andrewsargent2311-web/paraglide_vario_ESP32/paraglide_vario_ESP32/Goes into SD card/roy_real_crop_preview.png

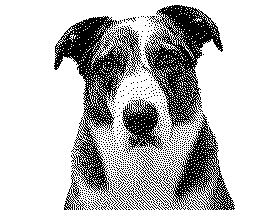
paraglide_vario_ESP32/Goes into SD card/roy_real_crop_preview.png
