andrewsargent2311-web/paraglide_vario_ESP32/Photos/20260914_193758.jpg

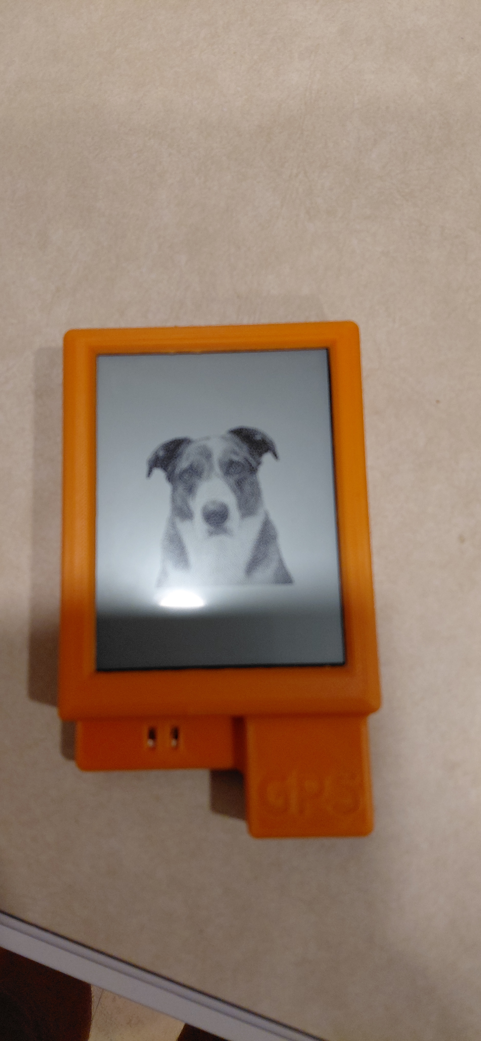
Photos/20260914_193758.jpg
