andrewsargent2311-web/paraglide_vario_ESP32/Photos/20260914_193810.jpg

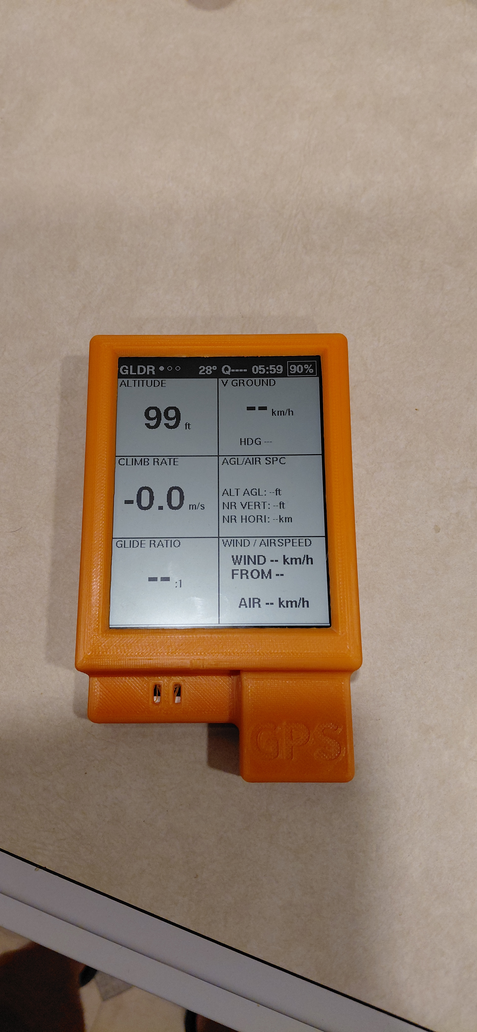
Photos/20260914_193810.jpg
