andrewsargent2311-web/paraglide_vario_ESP32/Photos/20260916_142536.jpg

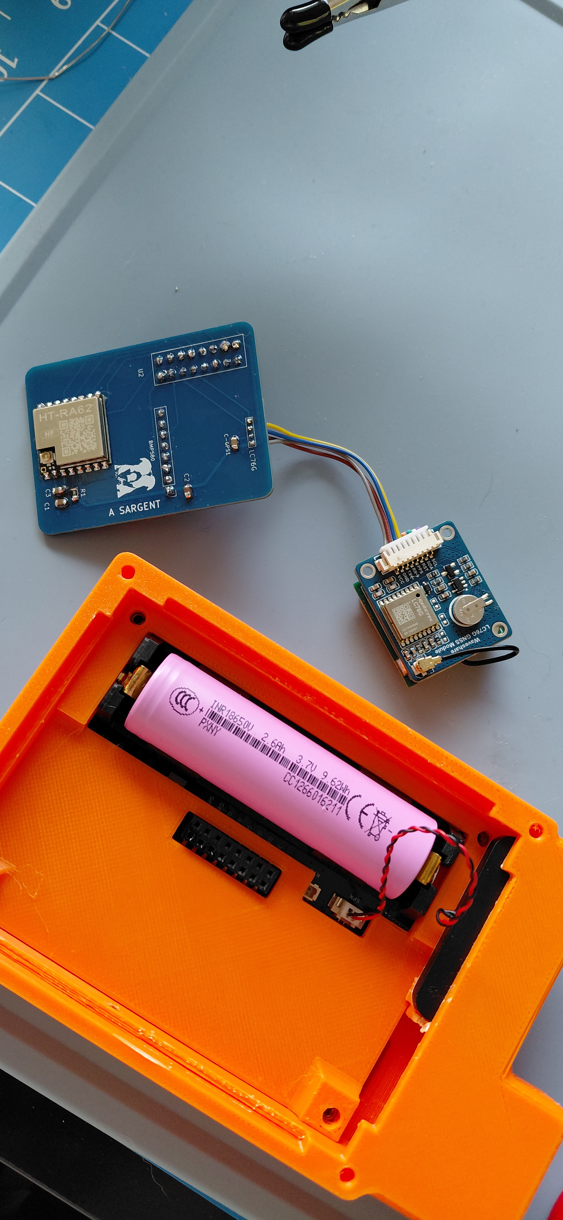
Photos/20260916_142536.jpg
