andrewsargent2311-web/paraglide_vario_ESP32/Photos/20260917_093752.jpg

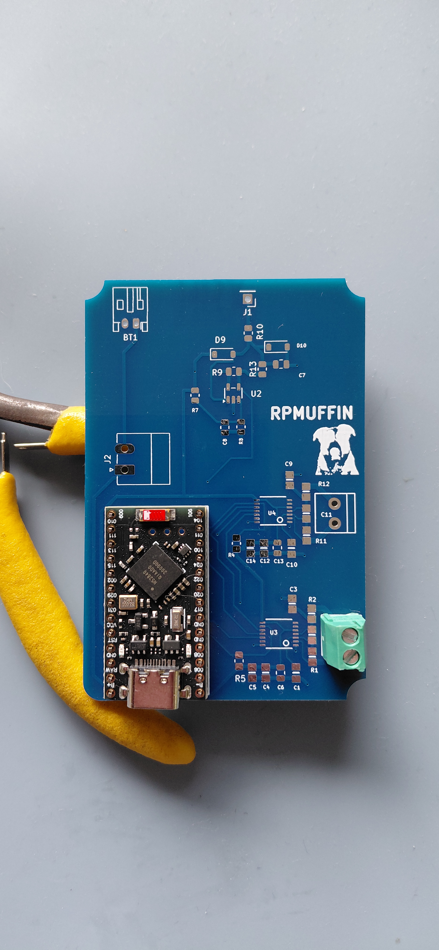
Photos/20260917_093752.jpg
