andrewsargent2311-web/paraglide_vario_ESP32/Photos/20260919_101642.jpg

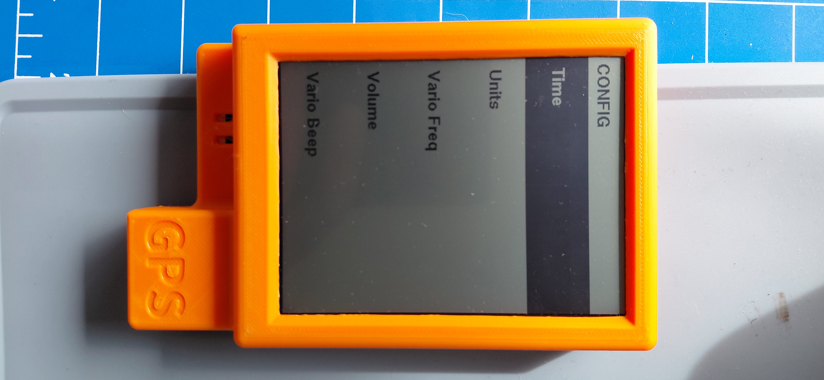
Photos/20260919_101642.jpg
