andrewsargent2311-web/paraglide_vario_ESP32/paraglide_vario_ESP32/menu.h

#ifndef MENU_H
#define MENU_H

#include <Arduino.h>
#include <U8g2lib.h>
#include "settings.h"

// =====================================================
// Display geometry. Duplicated (identically) from the main .ino so this
// header is self-contained -- see the derivation notes next to SCREEN_W/
// SCREEN_H in the .ino if that panel geometry ever changes.
// =====================================================
#define SCREEN_W 300
#define SCREEN_H 400

// =====================================================
// PAGES
// The actual page-drawing functions (drawParagliderPage() etc.) still live
// in the main .ino -- this type/state lives here because the menu needs to
// read and write it ("Main Page" submenu swaps the active main page).
// =====================================================
enum Page { PAGE_PARAGLIDER = 0,
            PAGE_WEATHER,
            PAGE_ADSB,
            PAGE_PARAMOTOR,
            PAGE_COUNT };

// Only 3 pages are cycled through with a short press. Slot 0 is the "main"
// page and is swappable between Paraglider and Paramotor from the menu;
// slots 1 and 2 are fixed at Weather and ADS-B.
#define ACTIVE_PAGE_COUNT 3

extern Page currentPage;
extern const char* PAGE_NAMES[PAGE_COUNT];
extern Page activePages[ACTIVE_PAGE_COUNT];
extern uint8_t activePageIndex;

// =====================================================
// MENU SCREENS
// The menu is a small tree, navigated with a stack (see menu.cpp):
//   MAIN
//   |-- MAIN_PAGE_SELECT  (Paraglider / Paramotor)
//   |-- CONFIG
//   |     |-- CONFIG_TIME     ("NZ (Auto)" DST-aware default, or a fixed
//   |     |                    manual UTC offset from -12 to +14 hours)
//   |     |-- UNITS           (Altitude / Speed, cycled in place)
//   |     |-- CONFIG_VOLUME   (main buzzer volume, 10-100% in 10% steps,
//   |     |                    dB-scaled: 100% = +12dB, 3dB per step)
//   |     |-- VARIO_BEEP
//   |     |     |-- VARIO_BEEP_CLIMB_VOL   (climb beep volume, 0-100%
//   |     |     |                           in 10% steps, dB-scaled)
//   |     |     `-- VARIO_BEEP_SINK_VOL    (sink tone volume, same scale)
//   |     `-- SCREEN          ("GPS Top" / "GPS Bottom" -- 180-degree
//   |                          display flip; see applyScreenOrientation())
//   |-- CONNECTIONS
//   |     |-- WIFI              (On/Off toggle, cycled in place --
//   |     |                      persisted; see setWifiRadioEnabled()
//   |     |                      (wifi_manager.h) -- then pick a saved
//   |     |                      network -- see secrets.h; choice is
//   |     |                      remembered across reboots)
//   |     |-- BLUETOOTH
//   |     |     |-- (On/Off toggle, cycled in place)
//   |     |     |-- SCAN        (live-updating list of nearby BLE
//   |     |     |                devices -- select one to connect; this
//   |     |     |                board is BLE-only, no Classic BT)
//   |     |     `-- (Forget Device -- only actionable once one's saved)
//   |     `-- FANET            (On/Off, cycled in place -- actually
//   |                            sleeps/wakes the SX1262, not just the
//   |                            software stack; see setFanetEnabled())
//   |-- FANET_MESSAGING  (On/Off toggle, persisted; see
//   |                      fanetMessagingEnabled in settings.h --
//   |                      plus one item per preset message,
//   |                      selecting one broadcasts it
//   |                      immediately. Broadcast only, no
//   |                      addressed messages -- see
//   |                      FanetMessaging.h/Fanet.h. Preset
//   |                      wording is compiled-in, not editable
//   |                      from the device -- no keyboard)
//   |-- MAP                (list of *.ADEM files found on the SD card)
//   |-- ADSB_SETTINGS
//   |     |-- ADSB_RADIUS       (horizontal alert trigger distance)
//   |     |-- ADSB_VERTICAL     (vertical alert trigger distance)
//   |     |-- (Auto-Jump toggle, cycled in place)
//   |     |-- (Alarm Sound: Off/Alarm/Voice, cycled in place -- see
//   |     |    adsbAlarmMode in settings.h. Alarm is the existing 5s
//   |     |    two-tone siren; Voice speaks the nearest threat's clock
//   |     |    position, heading, altitude and distance instead -- see
//   |     |    triggerAdsbAlert()/VoiceAlert.h)
//   |     |-- ADSB_ALERT_VOLUME (0-100% in 10% steps, same dB scale as
//   |     |                      the vario volumes, plus a Test item
//   |     |                      that previews whichever of Alarm/Voice
//   |     |                      is currently selected at this volume)
//   |     |-- ADSB_RANGE_RINGS  (far/default range ring pair -- 15/30km,
//   |     |                      10/20km, 20/40km, or 30/60km)
//   |     |-- (Airspace Alert Bar toggle, cycled in place -- NOT
//   |     |    persisted, always back on at reboot; see
//   |     |    airspaceAlertBarEnabled in settings.h)
//   |     `-- (Airspace Info toggle, cycled in place -- persisted; see
//   |          airspaceInfoBarEnabled in settings.h. Shows/hides
//   |          drawAirspaceInfoBar() -- ADS-B page only, bottom of
//   |          screen, current airspace name/frequency including CFZ,
//   |          or "Class G" if not inside anything charted)
//   |-- WEATHER_SETTINGS
//   |     |-- WEATHER_POLL_INTERVAL   (Zephyr station poll cadence)
//   |     |-- WEATHER_STATIONS_SHOWN  (how many stations to display)
//   |     `-- WEATHER_SOURCE          ("FANET" / "Zephyr" -- preferred
//   |                                  Weather-page data source; falls
//   |                                  back to FANET regardless if the
//   |                                  preferred source has no data)
//   `-- FLIGHT_RECORDINGS
//         |-- (Recording toggle, cycled in place -- NOT persisted,
//         |    always back on at reboot; see flightRecorderEnabled in
//         |    settings.h. OFF cleanly closes any in-progress IGC file
//         |    rather than abandoning it -- see setFlightRecorderEnabled())
//         |-- EXPORT_FILES     (Start/Stop a read-only WiFi file server
//         |                      for downloading IGC logs -- see
//         |                      FileServer.h. Needs WiFi connected
//         |                      (Connections > WiFi) and the SD card
//         |                      mounted; shows the URL to browse to
//         |                      once running. Auto-stops after 15
//         |                      minutes idle -- see
//         |                      FILE_SERVER_IDLE_TIMEOUT_MS)
//         `-- (Auto-Stop toggle, cycled in place -- persisted, off by
//              default; see igcAutoStopEnabled in settings.h. When on,
//              recording stops itself once ground speed has stayed
//              below 5km/h for 20s -- see IGC_AUTOSTOP_SPEED_KPH /
//              IGC_AUTOSTOP_SUSTAIN_MS, main .ino)
//
// Gestures (see updatePageButton() in the main .ino):
//   short press  -- move the highlight down (wraps within the current screen)
//   hold 2s      -- select the highlighted item (enter a submenu, apply a
//                   value, or toggle a setting)
//   double press -- go back one level, or close the menu from the top level
// =====================================================
enum MenuScreen {
  MENU_SCREEN_MAIN = 0,
  MENU_SCREEN_MAIN_PAGE_SELECT,
  MENU_SCREEN_CONFIG,
  MENU_SCREEN_CONFIG_TIME,
  MENU_SCREEN_UNITS,
  MENU_SCREEN_CONFIG_VOLUME,
  MENU_SCREEN_VARIO_BEEP,
  MENU_SCREEN_VARIO_BEEP_CLIMB_VOL,
  MENU_SCREEN_VARIO_BEEP_SINK_VOL,
  MENU_SCREEN_SCREEN,
  MENU_SCREEN_CONNECTIONS,
  MENU_SCREEN_WIFI_LIST,
  MENU_SCREEN_BLUETOOTH,
  MENU_SCREEN_BLUETOOTH_SCAN,
  MENU_SCREEN_MAP,
  MENU_SCREEN_ADSB_SETTINGS,
  MENU_SCREEN_ADSB_RADIUS,
  MENU_SCREEN_ADSB_VERTICAL,
  MENU_SCREEN_ADSB_ALERT_VOLUME,
  MENU_SCREEN_ADSB_RANGE_RINGS,
  MENU_SCREEN_WEATHER_SETTINGS,
  MENU_SCREEN_WEATHER_POLL_INTERVAL,
  MENU_SCREEN_WEATHER_STATIONS_SHOWN,
  MENU_SCREEN_WEATHER_SOURCE,
  MENU_SCREEN_FLIGHT_RECORDINGS,
  MENU_SCREEN_EXPORT_FILES,
  MENU_SCREEN_FANET_MESSAGING
};

extern bool menuActive;
extern uint8_t menuSelectedIndex;

// A "double press" is two presses with less than this many ms between the
// first release and the second press-down; a 2s hold on an open menu
// selects the highlighted item. Consumed by updatePageButton() in the
// main .ino.
#define MENU_DOUBLE_PRESS_MS 800
#define MENU_SELECT_HOLD_MS 2000

// =====================================================
// MAP FILE SELECTION
// The Map screen scans the SD card root for *.ADEM tiles when opened (see
// scanMapFiles() in menu.cpp) and lets the pilot choose which one
// getGroundElevationM() should read from. selectedDemFile (DEM_FILENAME_MAX_LEN
// too) now lives in settings.h alongside every other persisted setting --
// this header pulls both in via the settings.h include above. It's read
// by the DEM lookup in the main .ino's background task, guarded by
// sdMutex -- always go through setSelectedDemFile() to change it, never
// assign it directly, or a scan running on the other core could read a
// half-written filename.
// =====================================================
void setSelectedDemFile(const char* filename);

// =====================================================
// Dependencies provided by the main .ino
// =====================================================
extern U8G2_ST7305_300X400_1_4W_HW_SPI u8g2;
extern bool sdCardOK;
extern SemaphoreHandle_t sdMutex;

// Set whenever page/menu state changes; drives an immediate redraw instead
// of waiting for the next 1Hz display tick.
extern bool displayDirty;

// Short non-blocking UI feedback tone (defined in the main .ino).
void playFeedbackTone(float freq, unsigned long durationMs);

// Same as playFeedbackTone(), but at the loudness that a climb/sink volume
// percentage (0-100) would produce -- lets Config > Vario Beep play the
// tone back at the level being picked (defined in the main .ino).
void playVolumePreviewTone(float freq, unsigned long durationMs, uint8_t volumePercent);

// Re-applies buzzerVolumePercent (settings.h) to the ES8311 codec's
// volume register -- call after changing it so the new level takes
// effect immediately (defined in the main .ino).
void applyBuzzerVolume();

// Actually enables/disables the SX1262 radio to match fanetEnabled
// (settings.h) -- sleeps/wakes the chip itself, not just the software
// FANET stack. If the radio was never successfully initialised (e.g. it
// was off at boot), enabling runs the full init sequence for the first
// time. Call after changing fanetEnabled so it takes effect immediately
// (defined in the main .ino).
void setFanetEnabled(bool enabled);

// Re-applies screenOrientation (settings.h) to the physical display via
// u8g2.setDisplayRotation() -- call after changing it so the flip takes
// effect immediately (defined in the main .ino).
void applyScreenOrientation();

// Turns the IGC flight recorder on/off (Flight Recordings > Recording).
// OFF cleanly closes any in-progress recording (see stopIgcRecording())
// rather than leaving the file open-but-dangling -- updateIgcRecorder()
// itself is gated on flightRecorderEnabled and would otherwise just stop
// being called at all, without ever reaching its normal
// landing-detected close path. Does NOT persist -- flightRecorderEnabled
// (settings.h) always resets to true at boot, same reasoning as
// airspaceAlertBarEnabled, so a flight can never go unrecorded just
// because recording was switched off during ground testing and never
// switched back on. Call after changing flightRecorderEnabled so it
// takes effect immediately (defined in the main .ino).
void setFlightRecorderEnabled(bool enabled);

// =====================================================
// Menu functions
// =====================================================
void openMenu();
void closeMenu();
void menuMoveDown();
void menuSelectCurrentItem();
void menuGoBack();
void drawMenu();

#endif  // MENU_H
