andrewsargent2311-web/paraglide_vario_ESP32/paraglide_vario_ESP32/settings.cpp

#include "settings.h"
#include <Preferences.h>

static Preferences prefs;

// Defaults match the values the display code used to have hard-coded:
// altitude in feet, ground speed in km/h.
AltitudeUnit altitudeUnit = ALT_UNIT_FEET;
SpeedUnit speedUnit = SPEED_UNIT_KMH;

// Default matches the app's original behaviour: automatic NZ time with
// DST applied. utcOffsetHours only takes effect once the pilot picks a
// manual entry from the Time menu.
TimeZoneMode timeZoneMode = TZ_MODE_AUTO_NZ;
int8_t utcOffsetHours = 12;

void getPilotLocalTime(struct tm* outTm) {
  time_t now;
  time(&now);

  if (timeZoneMode == TZ_MODE_MANUAL) {
    // Shift the UTC epoch by the fixed offset and read it back out with
    // gmtime_r() (not localtime_r()) so the NZ_TIMEZONE DST rule set at
    // boot never gets applied on top of it.
    time_t shifted = now + (time_t)utcOffsetHours * 3600L;
    gmtime_r(&shifted, outTm);
  } else {
    // NZ_TIMEZONE (set once via setenv("TZ", ...) in the main .ino's
    // setup()) already encodes the DST transition rule, so localtime_r()
    // handles the adjustment automatically.
    localtime_r(&now, outTm);
  }
}

float altitudeToDisplay(float meters) {
  return (altitudeUnit == ALT_UNIT_FEET) ? (meters * 3.28084f) : meters;
}

const char* altitudeUnitLabel() {
  return (altitudeUnit == ALT_UNIT_FEET) ? "ft" : "m";
}

float speedKphToDisplay(float kph) {
  switch (speedUnit) {
    case SPEED_UNIT_MS: return kph / 3.6f;
    case SPEED_UNIT_MPH: return kph * 0.621371f;
    default: return kph;  // SPEED_UNIT_KMH
  }
}

const char* speedUnitLabel() {
  switch (speedUnit) {
    case SPEED_UNIT_MS: return "m/s";
    case SPEED_UNIT_MPH: return "mph";
    default: return "km/h";  // SPEED_UNIT_KMH
  }
}

// Defaults match the values that used to be hard-coded (100/500/100/400).
unsigned long climbGapMinMs = 100UL;
unsigned long climbGapMaxMs = 500UL;
unsigned long climbPulseMinMs = 100UL;
unsigned long climbPulseMaxMs = 400UL;

// Default approximates the original hard-coded ES8311 register value
// (0xBF of 0xFF, ~75%) at the nearest 20% step.
uint8_t buzzerVolumePercent = 80;

// Defaults match the values that used to be hard-coded: 5km/2000ft threat
// trigger, auto-jump on, alarm audible, weather polled every 5 minutes,
// 4 stations shown.
float adsbAlertRadiusKm = 5.0f;
float adsbAlertVerticalFt = 2000.0f;
bool adsbAutoJumpEnabled = true;
uint8_t adsbAlarmMode = ADSB_ALARM_TONE;  // preserves the old default (alarm audible, not muted)
uint8_t adsbAlertVolumePercent = 100;

// Deliberately NOT persisted -- see the comment in settings.h. Always
// starts true at boot.
bool airspaceAlertBarEnabled = true;

// Persisted (unlike airspaceAlertBarEnabled above) -- default on to
// match the app's original always-on airspace display behaviour.
bool airspaceInfoBarEnabled = true;

// Deliberately NOT persisted -- see the comment in settings.h. Always
// starts true at boot.
bool flightRecorderEnabled = true;

// Persisted (unlike flightRecorderEnabled above) -- off by default, an
// opt-in feature.
bool igcAutoStopEnabled = false;

// Default matches the original hardcoded far/default rings (30km outer,
// 15km inner).
float adsbRingOuterKm = 30.0f;
float adsbRingInnerKm = 15.0f;

unsigned long weatherPollIntervalMs = 5UL * 60UL * 1000UL;
uint8_t weatherStationsShown = 4;

// Default matches the app's original (WiFi/Zephyr-only) behaviour.
WeatherSource weatherSource = WEATHER_SOURCE_ZEPHYR;

bool buzzerMuted = false;

// Default: WiFi on, matching the app's original always-on behaviour.
bool wifiEnabled = true;

// Default matches the renamed tile now shipped on the SD card.
char selectedDemFile[DEM_FILENAME_MAX_LEN] = "/Lower_North_Island.ADEM";

// Default matches the app's original behaviour: boots on the Paraglider page.
uint8_t mainPageSelection = 0;  // 0 = Paraglider, 1 = Paramotor

// Default: radio on, matching the app's original always-on behaviour.
bool fanetEnabled = true;

// Default on -- matches fanetEnabled's default.
bool fanetMessagingEnabled = true;

// Default matches the app's original (and only, until now) orientation.
ScreenOrientation screenOrientation = SCREEN_ORIENTATION_GPS_BOTTOM;

// =====================================================
// PERSISTENCE
// =====================================================
void loadSettings() {
  prefs.begin("vario", false);

  altitudeUnit = (AltitudeUnit)prefs.getUChar("altUnit", (uint8_t)altitudeUnit);
  speedUnit = (SpeedUnit)prefs.getUChar("spdUnit", (uint8_t)speedUnit);

  timeZoneMode = (TimeZoneMode)prefs.getUChar("tzMode", (uint8_t)timeZoneMode);
  utcOffsetHours = (int8_t)prefs.getChar("utcOff", utcOffsetHours);

  climbGapMinMs = prefs.getUInt("gapMin", climbGapMinMs);
  climbGapMaxMs = prefs.getUInt("gapMax", climbGapMaxMs);
  climbPulseMinMs = prefs.getUInt("pulseMin", climbPulseMinMs);
  climbPulseMaxMs = prefs.getUInt("pulseMax", climbPulseMaxMs);

  buzzerVolumePercent = prefs.getUChar("volPct", buzzerVolumePercent);

  adsbAlertRadiusKm = prefs.getFloat("adsbRadius", adsbAlertRadiusKm);
  adsbAlertVerticalFt = prefs.getFloat("adsbVert", adsbAlertVerticalFt);
  adsbAutoJumpEnabled = prefs.getBool("adsbJump", adsbAutoJumpEnabled);
  adsbAlarmMode = prefs.getUChar("adsbAlarmMode", adsbAlarmMode);
  adsbAlertVolumePercent = prefs.getUChar("adsbAlertVol", adsbAlertVolumePercent);

  // Inner ring is always half of outer (see menu.cpp) -- only the outer
  // value is persisted, inner is re-derived here the same way.
  adsbRingOuterKm = prefs.getFloat("ringOuter", adsbRingOuterKm);
  adsbRingInnerKm = adsbRingOuterKm / 2.0f;

  weatherPollIntervalMs = prefs.getUInt("wxPoll", weatherPollIntervalMs);
  weatherStationsShown = prefs.getUChar("wxStations", weatherStationsShown);
  weatherSource = (WeatherSource)prefs.getUChar("wxSource", (uint8_t)weatherSource);

  String dem = prefs.getString("demFile", selectedDemFile);
  strncpy(selectedDemFile, dem.c_str(), DEM_FILENAME_MAX_LEN - 1);
  selectedDemFile[DEM_FILENAME_MAX_LEN - 1] = '\0';

  mainPageSelection = prefs.getUChar("mainPage", mainPageSelection);

  buzzerMuted = prefs.getBool("muted", buzzerMuted);
  wifiEnabled = prefs.getBool("wifiOn", wifiEnabled);

  fanetEnabled = prefs.getBool("fanetOn", fanetEnabled);
  fanetMessagingEnabled = prefs.getBool("fanetMsgOn", fanetMessagingEnabled);
  screenOrientation = (ScreenOrientation)prefs.getUChar("scrOrient", (uint8_t)screenOrientation);

  airspaceInfoBarEnabled = prefs.getBool("aspInfoBar", airspaceInfoBarEnabled);
  igcAutoStopEnabled = prefs.getBool("igcAutoStop", igcAutoStopEnabled);

  // airspaceAlertBarEnabled and flightRecorderEnabled are intentionally
  // never read here -- see their comments in settings.h. Both keep
  // their compiled-in default (true) every boot.
}

void saveSettings() {
  prefs.putUChar("altUnit", (uint8_t)altitudeUnit);
  prefs.putUChar("spdUnit", (uint8_t)speedUnit);

  prefs.putUChar("tzMode", (uint8_t)timeZoneMode);
  prefs.putChar("utcOff", utcOffsetHours);

  prefs.putUInt("gapMin", climbGapMinMs);
  prefs.putUInt("gapMax", climbGapMaxMs);
  prefs.putUInt("pulseMin", climbPulseMinMs);
  prefs.putUInt("pulseMax", climbPulseMaxMs);

  prefs.putUChar("volPct", buzzerVolumePercent);

  prefs.putFloat("adsbRadius", adsbAlertRadiusKm);
  prefs.putFloat("adsbVert", adsbAlertVerticalFt);
  prefs.putBool("adsbJump", adsbAutoJumpEnabled);
  prefs.putUChar("adsbAlarmMode", adsbAlarmMode);
  prefs.putUChar("adsbAlertVol", adsbAlertVolumePercent);

  prefs.putFloat("ringOuter", adsbRingOuterKm);

  prefs.putUInt("wxPoll", weatherPollIntervalMs);
  prefs.putUChar("wxStations", weatherStationsShown);
  prefs.putUChar("wxSource", (uint8_t)weatherSource);

  prefs.putString("demFile", selectedDemFile);

  prefs.putUChar("mainPage", mainPageSelection);

  prefs.putBool("muted", buzzerMuted);
  prefs.putBool("wifiOn", wifiEnabled);

  prefs.putBool("fanetOn", fanetEnabled);
  prefs.putBool("fanetMsgOn", fanetMessagingEnabled);
  prefs.putUChar("scrOrient", (uint8_t)screenOrientation);

  prefs.putBool("aspInfoBar", airspaceInfoBarEnabled);
  prefs.putBool("igcAutoStop", igcAutoStopEnabled);

  // airspaceAlertBarEnabled and flightRecorderEnabled are intentionally
  // never written here -- see their comments in settings.h.
}
