andrewsargent2311-web/paraglide_vario_ESP32/paraglide_vario_ESP32/wifi_manager.h

#ifndef WIFI_MANAGER_H
#define WIFI_MANAGER_H

#include <Arduino.h>

// =====================================================
// WI-FI CONNECTION MANAGER
// Owns which saved network (secrets.h's WIFI_NETWORKS) is active,
// persists that choice to flash (NVS, via the Preferences library) so it
// survives a reboot, and owns the connect/retry state machine that used
// to live directly in the main .ino's setup()/backgroundTask().
// =====================================================

// True whenever WiFi.status() == WL_CONNECTED as of the last check --
// read by backgroundTask() to gate ADS-B/weather polling, exactly like
// the old global did.
extern volatile bool wifiConnected;

// Index into secrets.h's WIFI_NETWORKS of the network currently selected
// from the menu (persisted -- see loadWifiSettings()). Only ever change
// this via selectWifiNetwork(), never assign it directly, so the flash
// write and the reconnect attempt always happen together.
extern uint8_t selectedWifiIndex;

// Call once from setup(), before startWifiConnect(). Reads
// selectedWifiIndex back from flash (defaults to 0 -- the first slot --
// if nothing has been saved yet, e.g. first boot ever).
void loadWifiSettings();

// Non-blocking. Kicks off WiFi.begin() for whichever network is
// currently selected and returns immediately -- does NOT wait to find
// out whether the connection succeeds. wifiManagerLoop() (already
// polled continuously from backgroundTask() on Core 0) picks up the
// moment WiFi.status() flips to WL_CONNECTED and takes over retry duty
// from there. Safe to call from setup() without stalling boot -- this
// replaces the old connectSavedWifi(), which blocked setup() for up to
// WIFI_CONNECT_TIMEOUT_MS (10s) waiting for the connection.
void startWifiConnect();

// Non-blocking. Call this from backgroundTask()'s existing poll loop
// (same place the old inline retry block lived) -- reconnects a dropped
// connection using whatever's currently selected, with the same
// WIFI_RETRY_MS/MAX_WIFI_RETRIES backoff the old code had.
void wifiManagerLoop();

// Called by the menu (Connections > WiFi) when the pilot picks a
// different saved network. No-ops on an empty slot. Persists the new
// index to flash, then disconnects and kicks off a fresh (non-blocking)
// connect attempt -- wifiConnected will reflect the result once it lands.
// If the radio is currently off (wifiEnabled, settings.h), this also
// turns it back on -- see setWifiRadioEnabled() below.
void selectWifiNetwork(uint8_t index);

// Turns the WiFi radio itself fully on or off, keeping wifiConnected and
// the retry backoff consistent with reality -- this is what
// Connections > WiFi's On/Off toggle calls (menu.cpp already includes
// this header directly, no indirection through the main .ino needed).
// OFF disconnects immediately and puts the radio to sleep;
// wifiManagerLoop()'s retry logic checks wifiEnabled too, so it won't
// silently undo an OFF state on the next tick. ON resumes with a fresh
// (non-blocking) connect attempt via startWifiConnect(). Also called
// automatically by selectWifiNetwork() if the radio was off when a
// specific network gets picked, since that's a strong enough signal of
// intent to turn it back on.
void setWifiRadioEnabled(bool enabled);

#endif  // WIFI_MANAGER_H
